luisllamasbinaburo/OpenRobot_V2/Module_Expansion_Mosfet/Module_Expansion_Mosfet.png

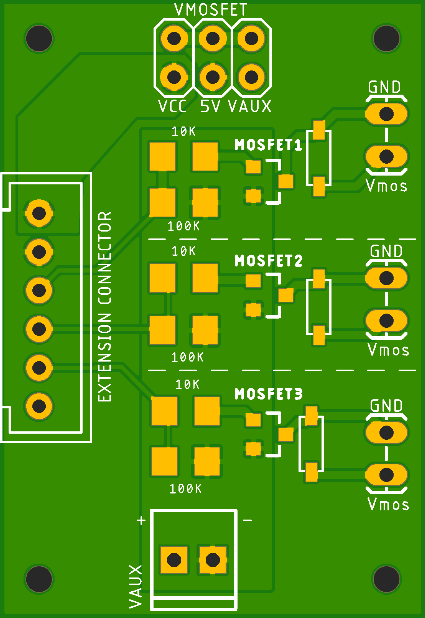
Module_Expansion_Mosfet/Module_Expansion_Mosfet.png
