luisllamasbinaburo/OpenRobot_V2/Module_I2C_TOF/Module_I2C_TOF.jpg

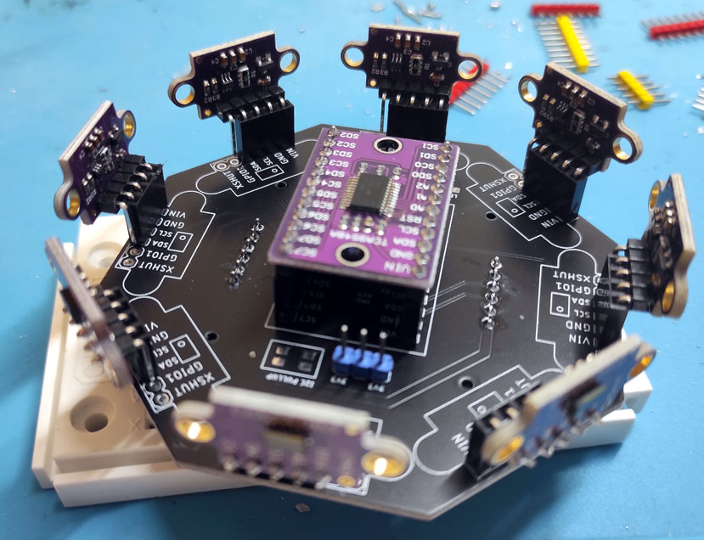
Module_I2C_TOF/Module_I2C_TOF.jpg
