luisllamasbinaburo/OpenRobot_V2/Module_MCU_ArduinoNano/Module_MCU_ArduinoNano.png

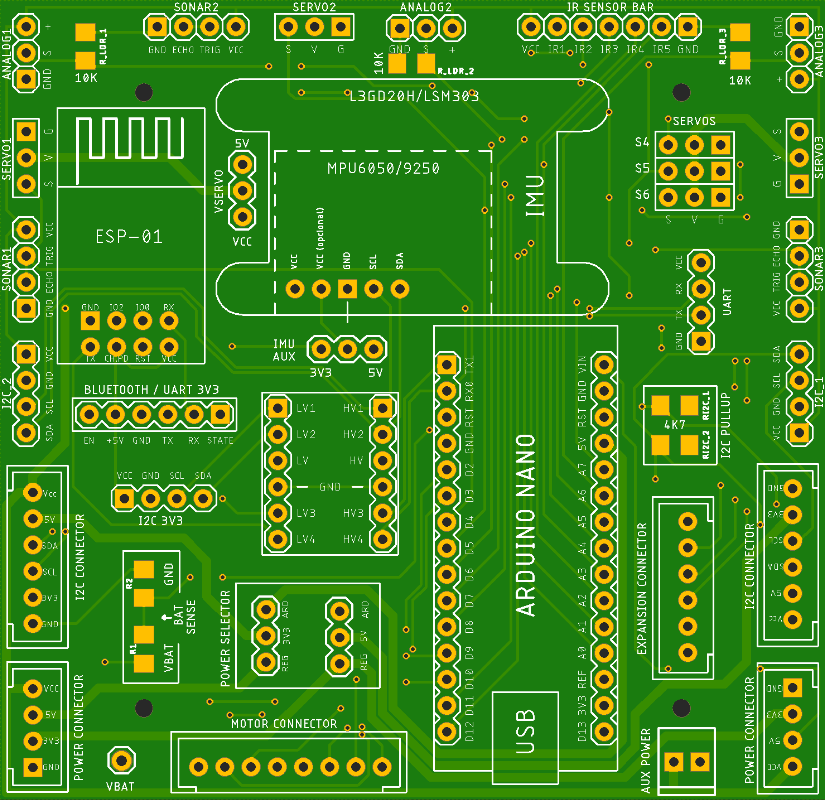
Module_MCU_ArduinoNano/Module_MCU_ArduinoNano.png
