luisllamasbinaburo/OpenRobot_V2/Module_MCU_ESP32Embed/Module_MCU_ESP32Embed.jpg

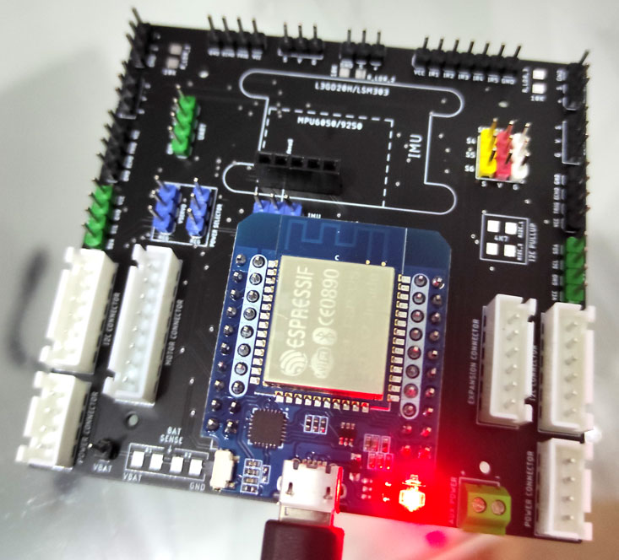
Module_MCU_ESP32Embed/Module_MCU_ESP32Embed.jpg
