luisllamasbinaburo/OpenRobot_V2/Module_MCU_ESP32Embed/Module_MCU_ESP32Embed.png

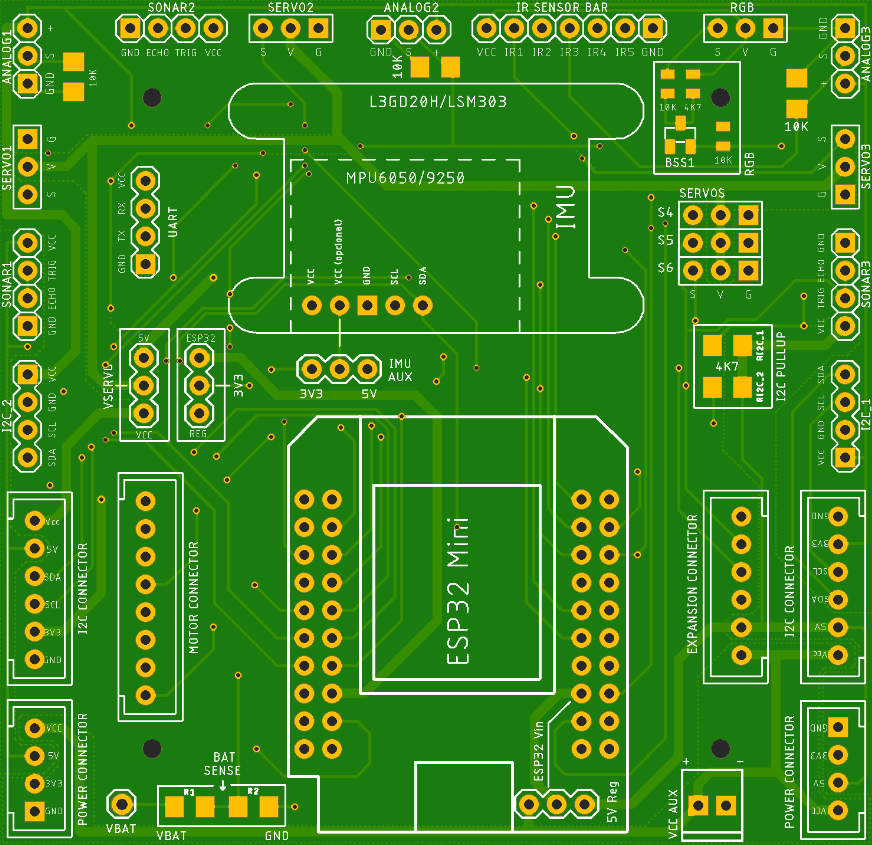
Module_MCU_ESP32Embed/Module_MCU_ESP32Embed.png
