luisllamasbinaburo/OpenRobot_V2/Module_MCU_M5Stack/Module_MCU_M5Stack.png

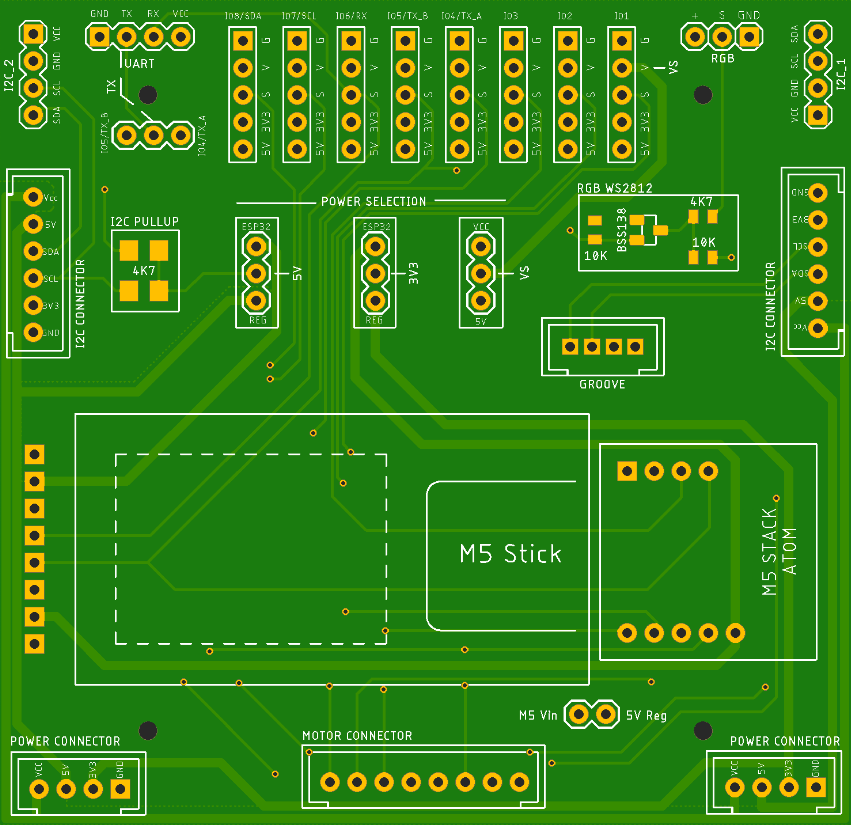
Module_MCU_M5Stack/Module_MCU_M5Stack.png
