luisllamasbinaburo/OpenRobot_V2/Module_MCU_M5Stack/Module_MCU_M5StackAtom.jpg

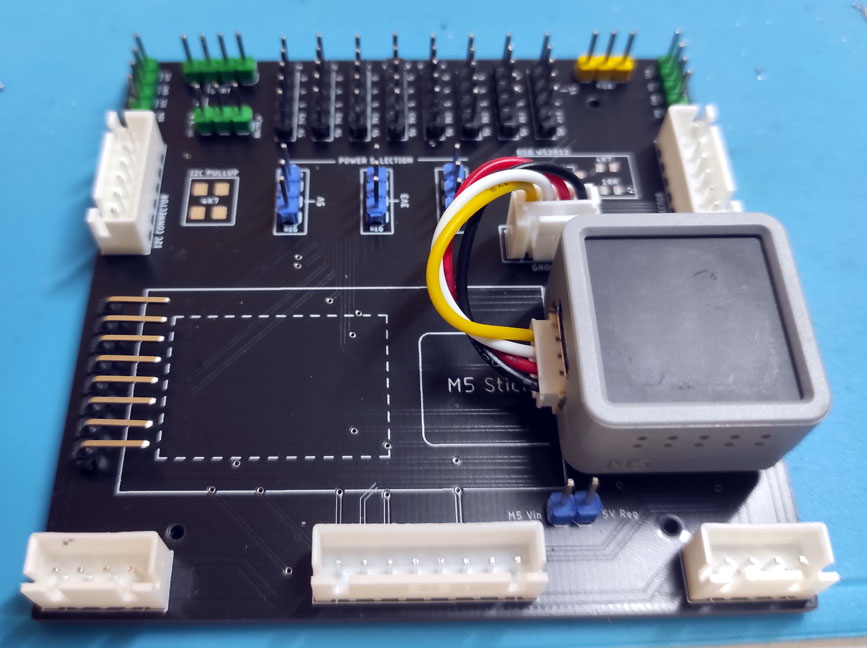
Module_MCU_M5Stack/Module_MCU_M5StackAtom.jpg
