luisllamasbinaburo/OpenRobot_V2/Module_Motor_DC/Module_Motor_DC.jpg

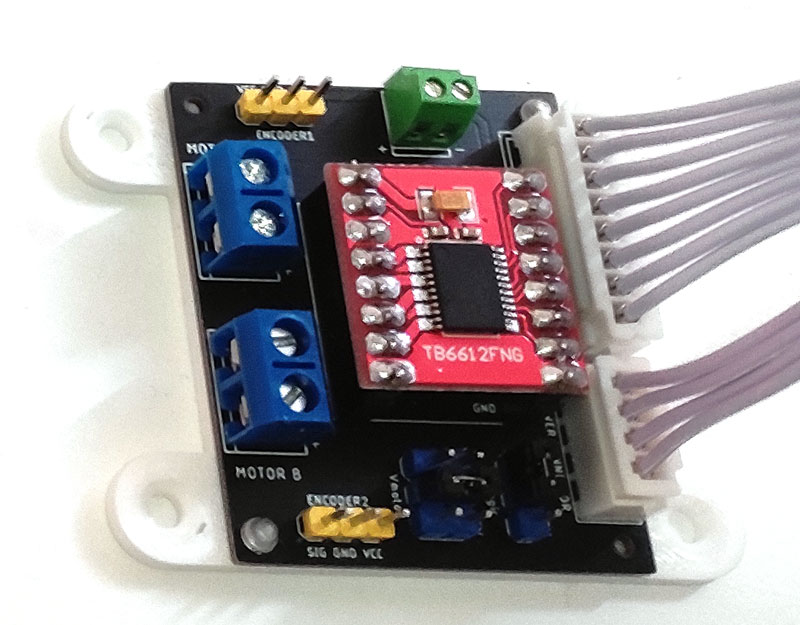
Module_Motor_DC/Module_Motor_DC.jpg
