luisllamasbinaburo/OpenRobot_V2/Module_Motor_DC/Module_Motor_DC.png

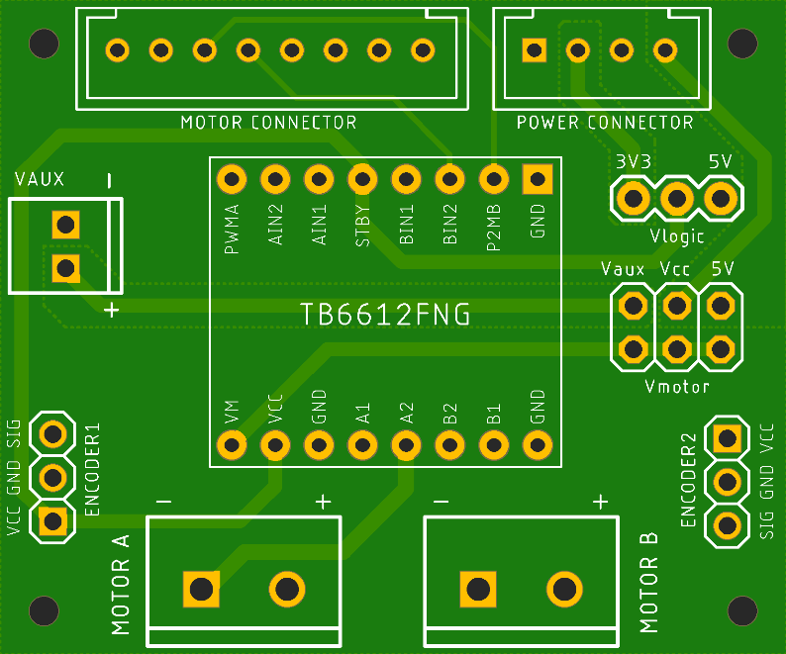
Module_Motor_DC/Module_Motor_DC.png
