luisllamasbinaburo/OpenRobot_V2/Module_Motor_Stepper/Module_Motor_Stepper.png

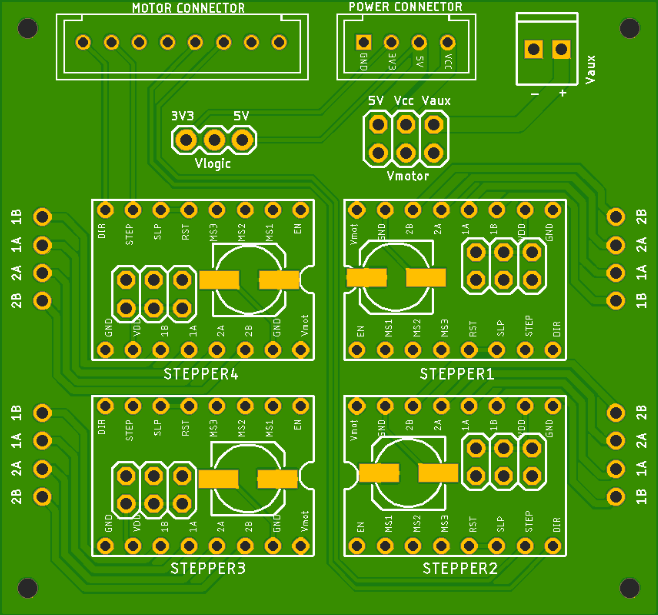
Module_Motor_Stepper/Module_Motor_Stepper.png
