luisllamasbinaburo/OpenRobot_V2/Module_PowerSource/Module_PowerSource.jpg

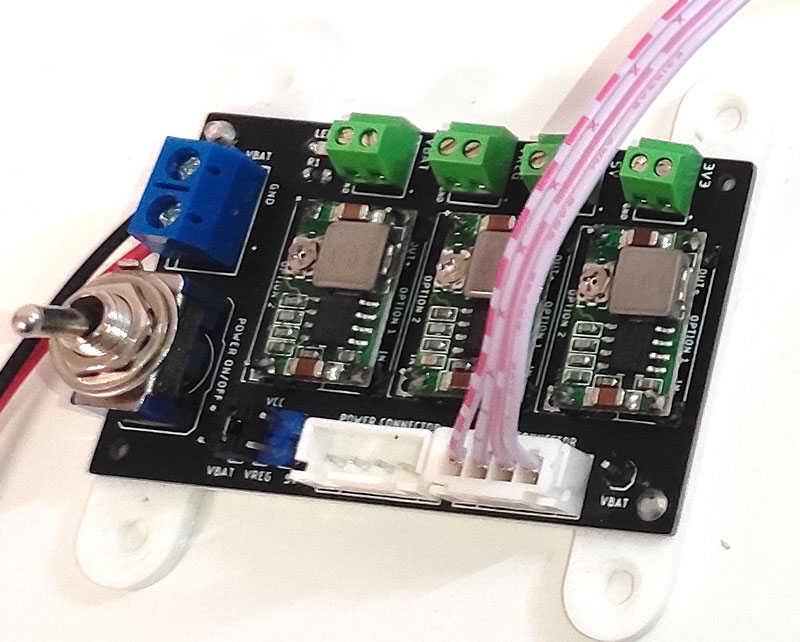
Module_PowerSource/Module_PowerSource.jpg
