luisllamasbinaburo/OpenRobot_V2/Module_PowerSource/Module_PowerSource.png

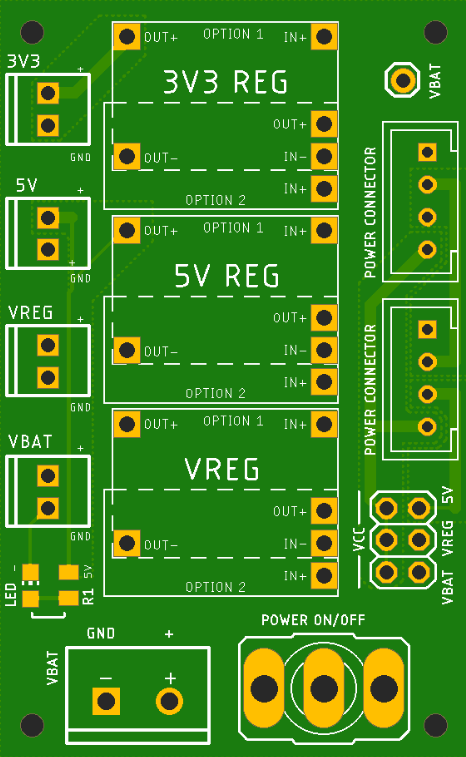
Module_PowerSource/Module_PowerSource.png
